asdfgh0318/space-station/radio-telescope-plan-images/page-03.jpg

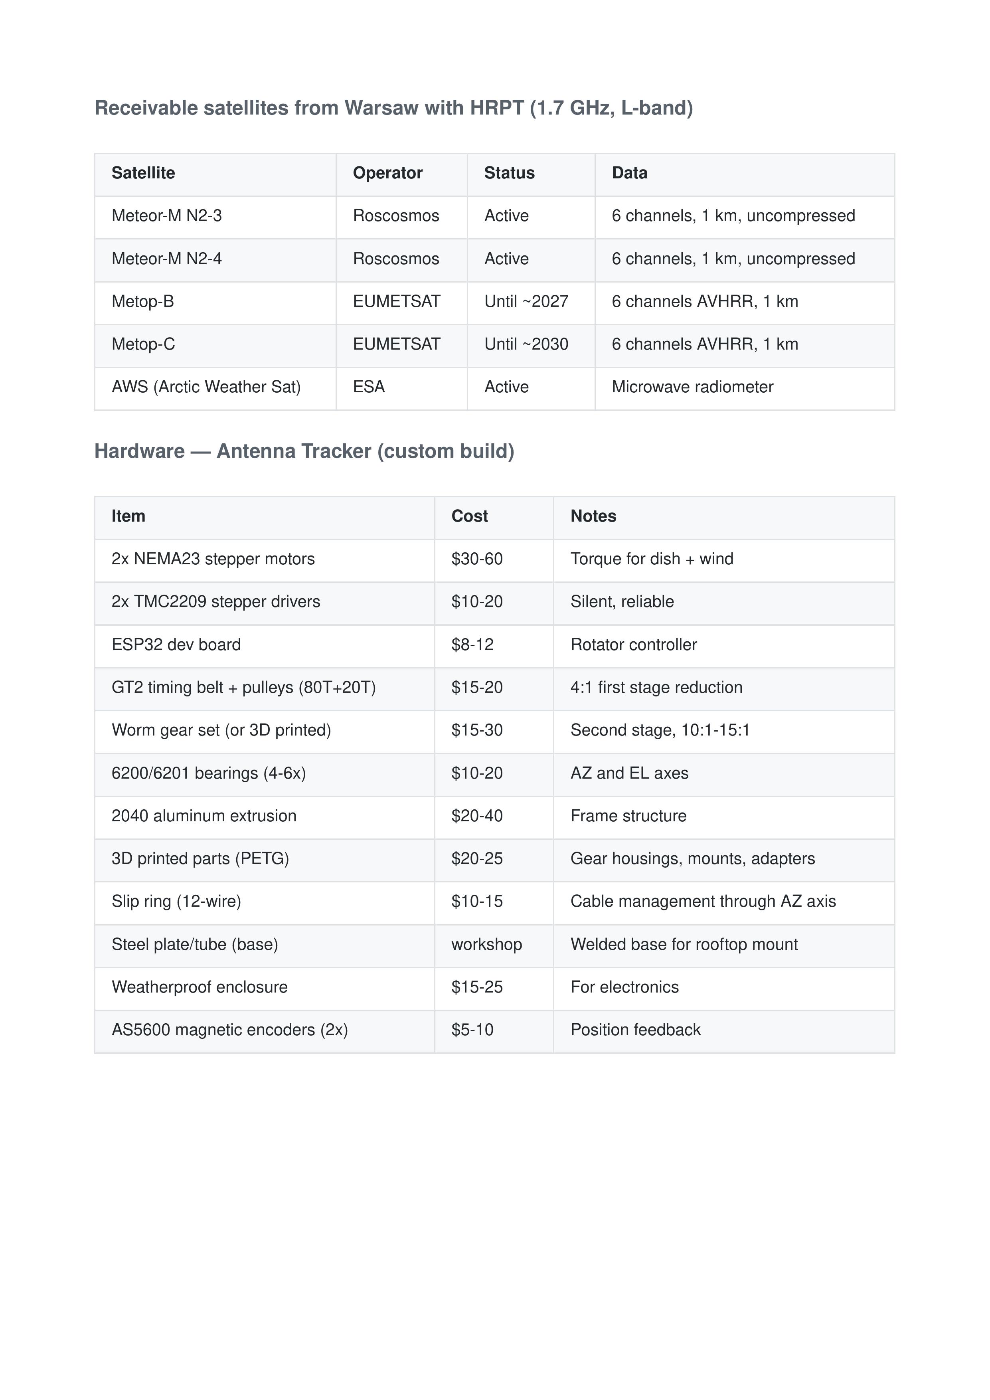
radio-telescope-plan-images/page-03.jpg
