asdfgh0318/space-station/radio-telescope-plan-images/page-04.jpg

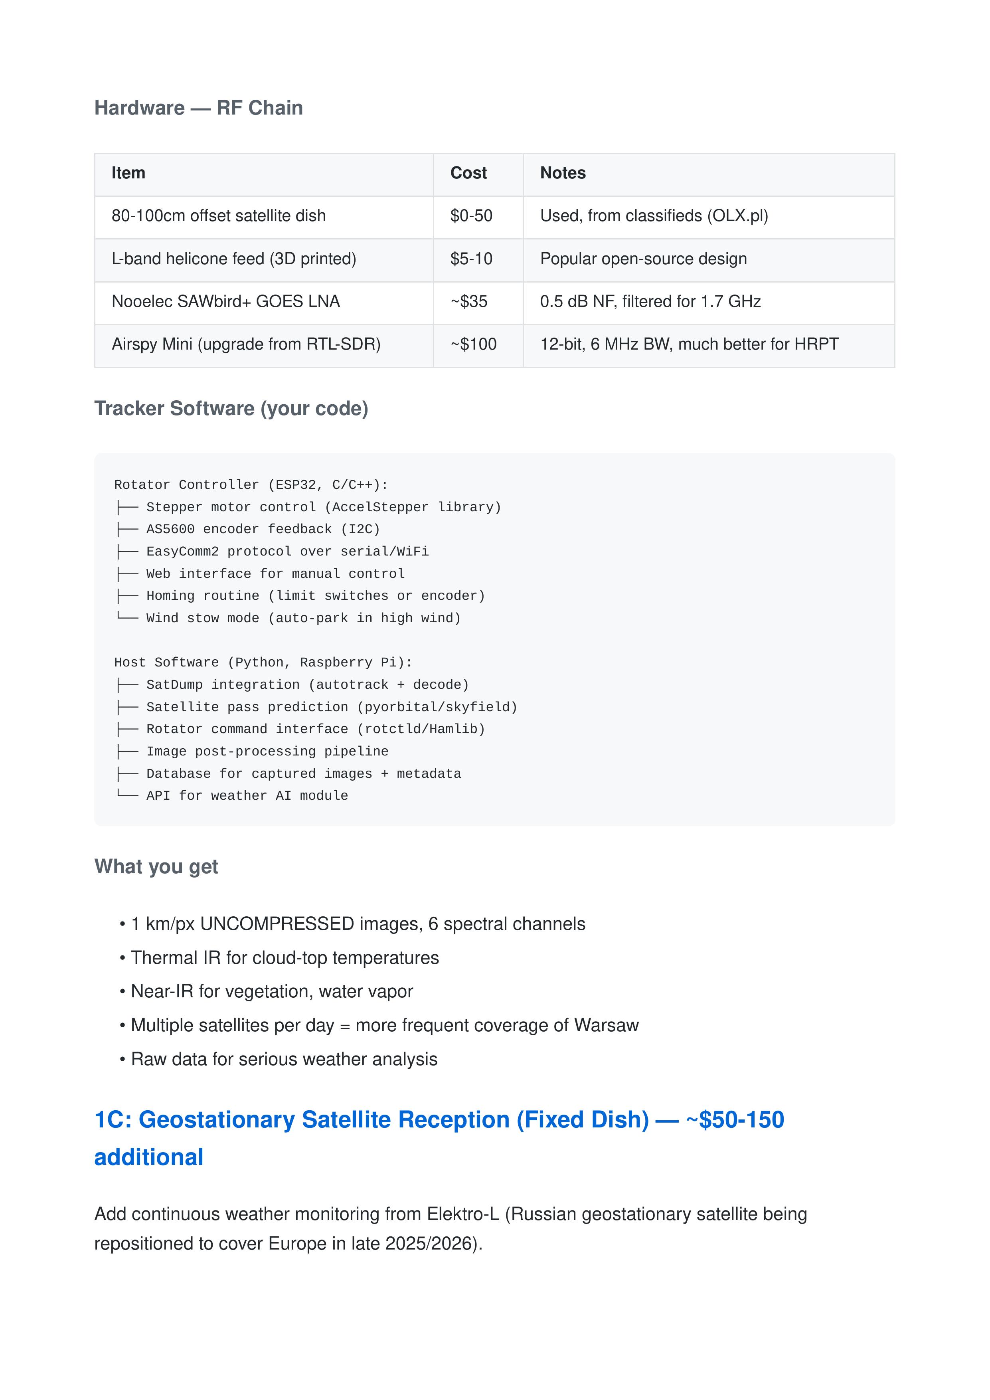
radio-telescope-plan-images/page-04.jpg
