asdfgh0318/space-station/radio-telescope-plan-images/page-05.jpg

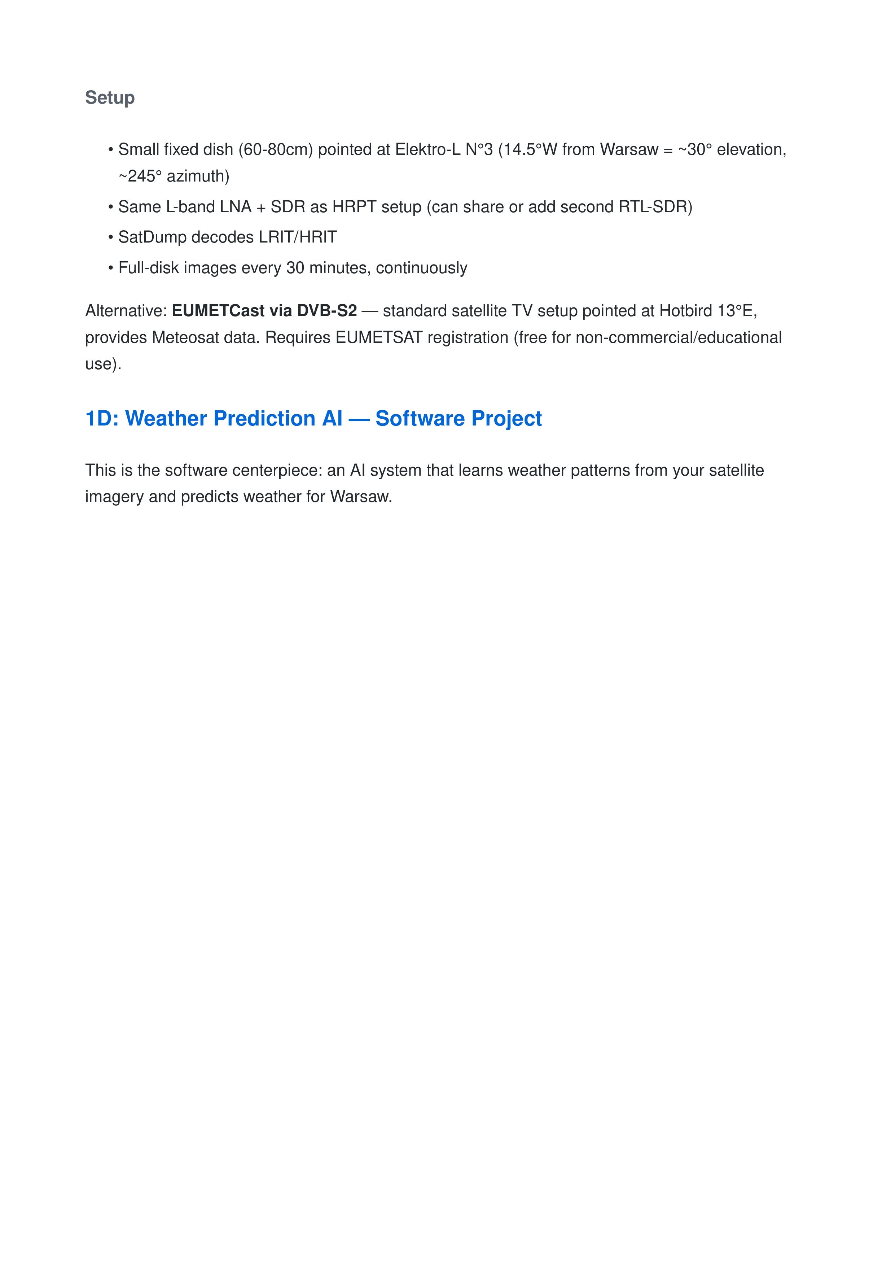
radio-telescope-plan-images/page-05.jpg
