asdfgh0318/space-station/radio-telescope-plan-images/page-07.jpg

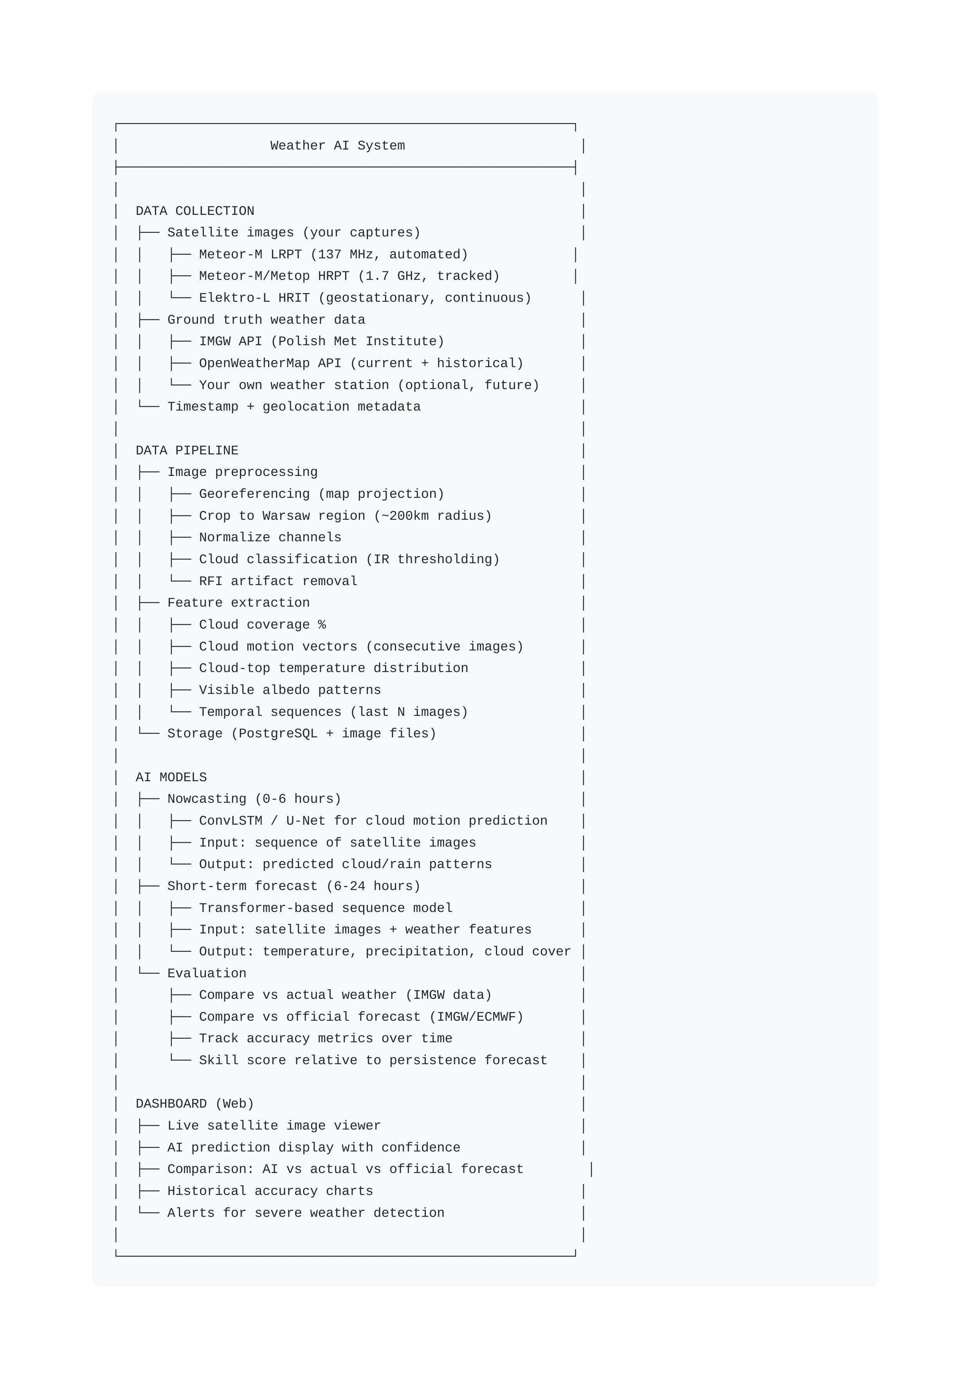
radio-telescope-plan-images/page-07.jpg
