asdfgh0318/space-station/radio-telescope-plan-images/page-08.jpg

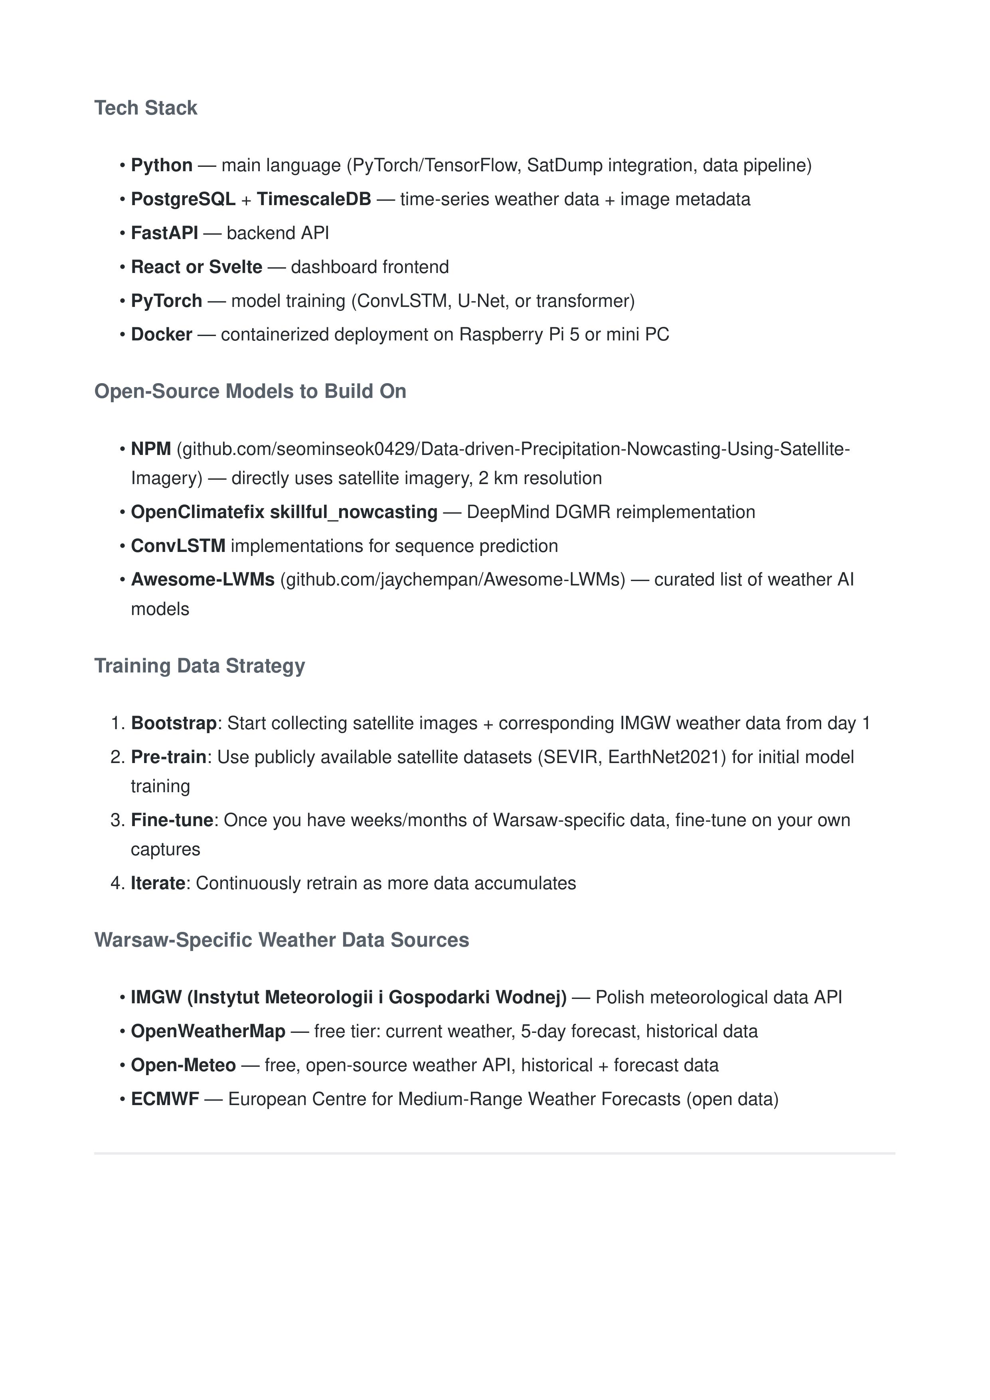
radio-telescope-plan-images/page-08.jpg
