asdfgh0318/space-station/radio-telescope-plan-images/page-12.jpg

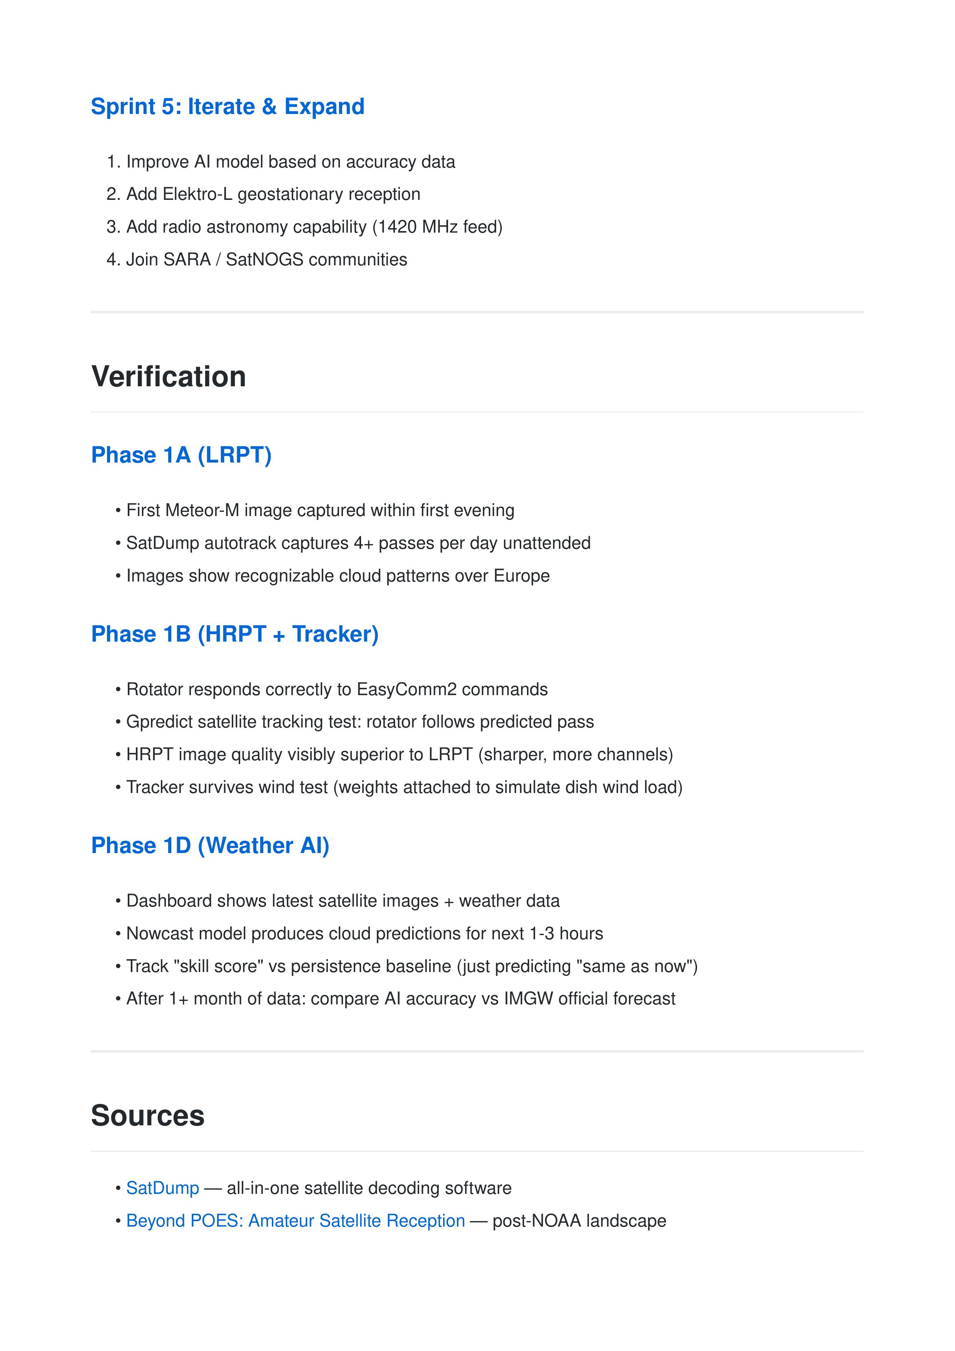
radio-telescope-plan-images/page-12.jpg
